dJOS1475/SmartWatch_Plus/Info/M27C256B.gif

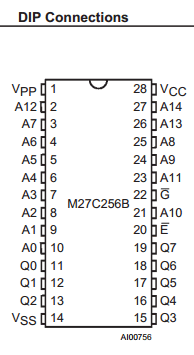
Info/M27C256B.gif
