dJOS1475/SmartWatch_Plus/Info/Screenshot 2019-10-07 15.33.27.png

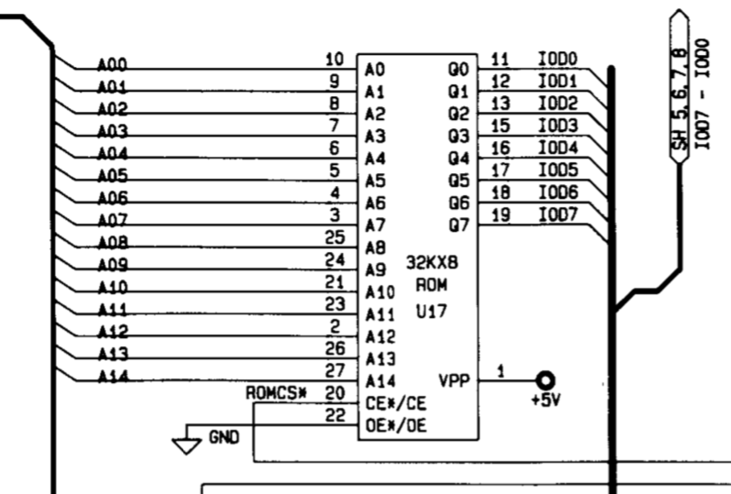
Info/Screenshot 2019-10-07 15.33.27.png
