dJOS1475/SmartWatch_Plus/Info/Screenshot 2019-10-07 15.34.11.png

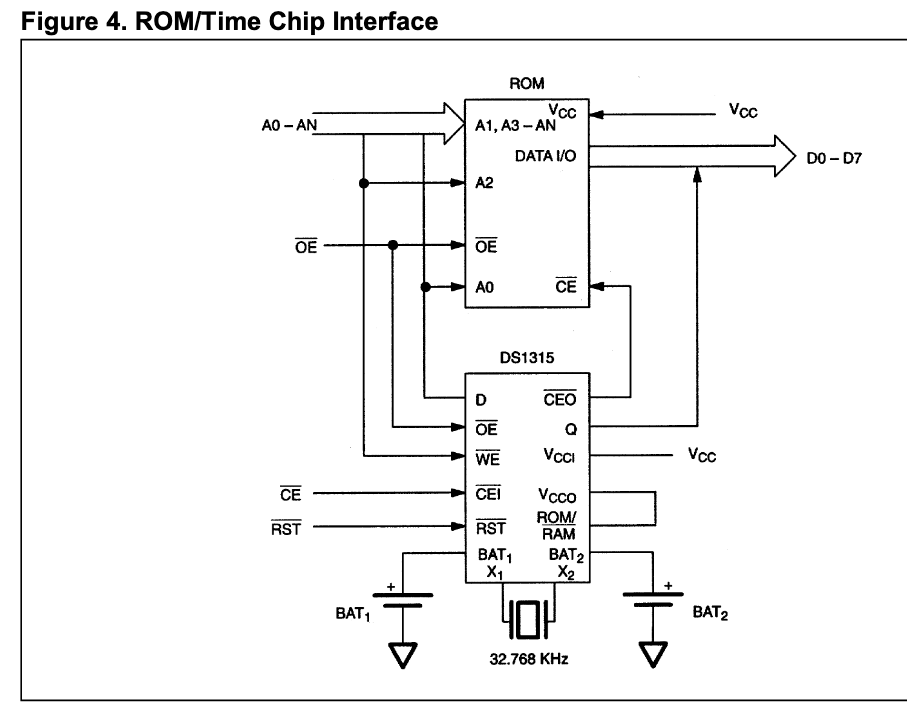
Info/Screenshot 2019-10-07 15.34.11.png
